LeeJaesung2/DBASEV/pixhawk/drone/roadData/real_test_data/road_id7_data.xlsx

road_id | waypoint_id | latitude(위도) | longtitude(경도) | altitude
7 | 1 | 35.1544175 | 128.1048654 | 3
7 | 2 | 35.1543759 | 128.1048862 | 3
7 | 3 | 35.1543342 | 128.104907 | 3
7 | 4 | 35.1542926 | 128.1049278 | 3
7 | 5 | 35.1542509 | 128.1049486 | 3
