LeeJaesung2/DBASEV/pixhawk/Documentation/3.getAttribute.py

# 속성 값 설명 링크 : https://dronekit-python.readthedocs.io/en/latest/automodule.html#dronekit.Vehicle.armed
from dronekit import connect, VehicleMode
import time

# 기본 시작 코드
vehicle = connect("/dev/ttyAMA0", wait_ready=True, baud=57600)
vehicle.mode = VehicleMode("GUIDED")
vehicle.armed = True
while not vehicle.mode.name =='GUIDED' and not vehicle.armed and not api.exit:
    print (" Getting ready to take off ...")
    time.sleep(1)
    
# vehicle is an instance of the Vehicle class
print ("Autopilot Firmware version: %s" % vehicle.version)
print ("Autopilot capabilities (supports ftp): %s" % vehicle.capabilities.ftp)
print ("Global Location: %s" % vehicle.location.global_frame)
print ("Global Location (relative altitude): %s" % vehicle.location.global_relative_frame)
print ("Local Location: %s" % vehicle.location.local_frame)#NED
print ("Attitude: %s" % vehicle.attitude)
print ("Velocity: %s" % vehicle.velocity)
print ("GPS: %s" % vehicle.gps_0)
print ("Groundspeed: %s" % vehicle.groundspeed)
print ("Airspeed: %s" % vehicle.airspeed)
print ("Gimbal status: %s" % vehicle.gimbal)
print ("Battery: %s" % vehicle.battery)
print ("EKF OK?: %s" % vehicle.ekf_ok)
print ("Last Heartbeat: %s" % vehicle.last_heartbeat)
print ("Rangefinder: %s" % vehicle.rangefinder)
print ("Rangefinder distance: %s" % vehicle.rangefinder.distance)
print ("Rangefinder voltage: %s" % vehicle.rangefinder.voltage)
print ("Heading: %s" % vehicle.heading)
print ("Is Armable?: %s" % vehicle.is_armable)
print ("System status: %s" % vehicle.system_status.state)
print ("Mode: %s" % vehicle.mode.name) # settable
print ("Armed: %s" % vehicle.armed) # settable
