LeeJaesung2/DBASEV/python_src/finaltest.py

from main import init, update
from drone import Drone
from car import Car
import time

# straight
'''
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
    car_idx += 1

    update_time = time.time()
    log_data = "{},{},{},{},{},{},{},{}\n".format(update_time-starttime,car.velocity,car.road_id,car.waypoint,drone.velocity,drone.current_speed,drone.road_id,drone.target_waypoint)
    add_logfile(log_data)
    time.sleep(0.1)    
