LeeJaesung2/DBASEV/test/messageQueue/messageQueue.cpp

#include "messageQueue.h"
#include <Python.h>

#include <iostream> //cout
#include <string>
#include <cstring>
#include <cstdlib>
#include <unistd.h>
#include <sys/ipc.h>
#include <sys/msg.h>


#define BUFFER_SIZE 26

int pushcount = 0;
int fullcount = 0;

int callPython(const char *src,const char *func, int arg, ...){
    PyObject *pName, *pModule, *pFunc;
    PyObject *pArgs, *pValue;
    int i;

    Py_Initialize();
    PyRun_SimpleString("import sys");
    PyRun_SimpleString("sys.path.append(\".\")");
    pName = PyUnicode_DecodeFSDefault(src); //get python src

    /*Error checking of pName*/
    pModule = PyImport_Import(pName);
    Py_DECREF(pName);

    if (pModule != NULL) {
        pFunc = PyObject_GetAttrString(pModule, func);

        if (pFunc && PyCallable_Check(pFunc)) {

            va_list ap;
            va_start(ap,arg);
            pArgs = PyTuple_New(arg);
            for (i = 0; i < arg; ++i) {
                pValue = PyLong_FromLong(va_arg(ap,int));
                if (!pValue) {
                    Py_DECREF(pArgs);
                    Py_DECREF(pModule);
                    fprintf(stderr, "Cannot convert argument\n");
                    return 1;
                }
                /* pValue reference stolen here: */
                PyTuple_SetItem(pArgs, i, pValue);
            }
            pValue = PyObject_CallObject(pFunc, pArgs); // call function with argument
            Py_DECREF(pArgs);
            /*value checking*/
            if (pValue != NULL) {
                printf("Result of call: %ld\n", PyLong_AsLong(pValue));
                Py_DECREF(pValue);
            }
            /*No return value*/
            else {
                Py_DECREF(pFunc);
                Py_DECREF(pModule);
                PyErr_Print();
                fprintf(stderr,"Call failed\n");
                return 1;
            }
            va_end(ap);
        }
        else {
            if (PyErr_Occurred())
                PyErr_Print();
            fprintf(stderr, "Cannot find function \"%s\"\n", func);
        }
        Py_XDECREF(pFunc);
        Py_DECREF(pModule);
    }
    else {
        PyErr_Print();
        fprintf(stderr, "Failed to load \"%s\"\n", src);
        return 1;
    }
    Py_Finalize();
    return PyLong_AsLong(pValue);
    
}

using namespace std;

struct MsgBuf {
    long msgtype; // message type, must be > 0
    int value;
    char buf[BUFFER_SIZE];
};

int mq_init(key_t key){

    int key_id = msgget( key, IPC_CREAT|0666);
    if (key_id == -1) {
        cerr << "Message Get Failed!" << endl;
        exit(EXIT_FAILURE);
    }
    return key_id;
}

void push(int key_id,msqid_ds buf, MsgBuf msg){
    

    pushcount++;
    if (msgctl(key_id, IPC_STAT, &buf) == -1) {
        std::cerr << "Failed to get message queue status!" << std::endl;
        return;
    }
    //Check queue is full
    if (buf.msg_qnum >= 409) {
        std::cerr << "Message queue is full. Skipping message send." << std::endl;
        usleep(1);
        return;
    }
    // Check the number of messages currently in the queue
    printf("num of data in the queue is %ld\n",buf.msg_qnum);
    while (buf.msg_qnum >0 ) {
        // Remove existing message before pushing a new one
        if (msgrcv(key_id, &msg, sizeof(msg), 0, IPC_NOWAIT) == -1) {
            std::cerr << "Failed to remove existing message from the queue!" << std::endl;
            return;
        }
    }
    if (msgsnd(key_id, &msg, sizeof(msg), IPC_NOWAIT) == -1) {
            cerr << "Message Sending Failed!" << endl;
            exit(EXIT_FAILURE);
        }
}

void * comm(void *arg){
    int cnt = 0;
    MsgBuf msg;
    msg.msgtype = 1;
    int key_id = mq_init((key_t)5657);

    struct msqid_ds buf;
    while(1){
        msg.value = ++cnt;
        if (cnt >= 100000) {
            cout << "Message Sending Finished!" << endl;
            break;
        }
        strcpy(msg.buf, "Message received!]");
        push(key_id,buf, msg);
        cout << "value: " << msg.value << endl;
        //sleep(1);

    }
    //sleep(10);
    cout <<"full counter" << fullcount << endl;
    cout <<"push counter" << pushcount << endl;
    return 0;
}


void * producer(void *arg){
    // int cnt = 0;
    // int key_id;
    // MsgBuf msg;
    // msg.msgtype = 1;

    // key_id = msgget((key_t) 7777, IPC_CREAT|0666);
    // printf("queue key id is %d\n",key_id);
    // if (key_id == -1) {
    //     cerr << "Message Get Failed!" << endl;
    //     exit(EXIT_FAILURE);
    // }
    
    // while (1) {
    //     msg.value = ++cnt;
    
    //     if (cnt >= 10) {
    //         cout << "Message Sending Finished!" << endl;
    //         break;
    //     }
    //     strcpy(msg.buf, "Hello from C++ producer!");
    //     if (msgsnd(key_id, &msg, sizeof(msg), IPC_NOWAIT) == -1) {
    //         cerr << "Message Sending Failed!" << endl;
    //         exit(EXIT_FAILURE);
    //     }
        
    //     cout << "value: " << msg.value << endl;
    //     sleep(1);
    // }
    // exit(EXIT_SUCCESS);
     return 0;
}

void * consumer(void *arg){
    const char *src = "consumer";
    const char *func = "consumer";
    callPython(src, func, 1, 1);   
    return 0;
}
