LeeJaesung2/DBASEV/pixhawk/drone/pixhawk_test_files/test.py

from dronekit import connect, VehicleMode, LocationGlobalRelative, Command
from pymavlink import mavutil
import time
import argparse 
import dronekit_sitl

'''
parser = argparse.ArgumentParser(description='Print out vehicle state information. Connects to SITL on local PC by default.')
parser.add_argument('--connect', 
                help="vehicle connection target string. If not specified, SITL automatically started and used.")
args = parser.parse_args()

connection_string = args.connect
sitl = None

#Start SITL if no connection string specified
if not connection_string:
    sitl = dronekit_sitl.start_default()
    connection_string = sitl.connection_string()

print("\nConnecting to vehicle on: %s" % connection_string)
vehicle = connect(connection_string, wait_ready=True)

vehicle.wait_ready('autopilot_version')
'''

connection_string = 'udp:127.0.0.1:1450'
vehicle = connect(connection_string, wait_ready=True)
print("Connecting to vehicle on : %s" %(connection_string, ))
cmd = None

# takeoff function

def arm_and_takeoff_to_pixhawk(aTargetAltitude):
    """
    Arms vehicle and fly to aTargetAltitude.
    """

    print("Basic pre-arm checks")
    # Don't try to arm until autopilot is ready
    while not vehicle.is_armable:
        print(" Waiting for vehicle to initialise...")
        time.sleep(1)

    print("Arming motors")

    # Confirm vehicle armed before attempting to take off
    while not vehicle.armed:
        print(" Waiting for arming...")
        vehicle.mode = VehicleMode("GUIDED")
        
        vehicle.armed = True
        time.sleep(1)

    print("Taking off!")
    vehicle.simple_takeoff(aTargetAltitude)  # Take off to target altitude

    while True:
        print(" Altitude: ", vehicle.location.global_relative_frame.alt)
        if vehicle.location.global_relative_frame.alt >= aTargetAltitude * 0.95:
            print("Reached target altitude")
            break
        time.sleep(1)

def add_waypoints_to_pixhawk(waypoint_list):
    
    cmd = vehicle.commands
    
    for waypoint in waypoint_list:
        print("wapoint : ", waypoint[2], waypoint[3], waypoint[4])
        wp = LocationGlobalRelative(waypoint[2], waypoint[3], waypoint[4])
        cmd.add(
            Command(0,0,0, 
            mavutil.mavlink.MAV_FRAME_GLOBAL_RELATIVE_ALT,
            mavutil.mavlink.MAV_CMD_NAV_WAYPOINT,
            0, 1, 0, 0, 0, 0,
            wp.lat, wp.lon, wp.alt
            )
        )    
    cmd.upload()
    
    change_vehicleMode("AUTO")

    cmd.next = 0

def print_current_gps():
    current_gps = vehicle.location.global_frame
    print("위도: %.7f" % current_gps.lat)
    print("경도: %.7f" % current_gps.lon)
    print("고도: %.1f" % current_gps.alt)
    

def set_airspeed_to_pixhawk(airspeed):
    vehicle.groundspeed = airspeed


def change_vehicleMode(new_mode):
    while vehicle.mode.name != new_mode:
        print("Vehicl mode : ", vehicle.mode.name)
        print("Changing Vehcile mode to ", new_mode, "....")
        
        vehicle.mode = VehicleMode(new_mode)
        time.sleep(1)


def land_to_pixhawk(vehicle):
    vehicle.mode = VehicleMode("LAND") 
    while not vehicle.mode.name=='LAND':
        print("Waiting for drone to land...")
        time.sleep(1)

    vehicle.armed = False 
    vehicle.close() 

"""------------------------------------------------------------------------------------"""
'''
# curve course
waypoints = {1: [[1, 1, 35.1535098, 128.1002861, 5.0], [1, 2, 35.1535017, 128.1003405, 5.0], [1, 3, 35.153494, 128.1003952, 5.0], [1, 4, 
35.1534847, 128.1004491, 5.0], [1, 5, 35.153477, 128.1005038, 5.0], [1, 6, 35.1534693, 128.1005578, 5.0], [1, 7, 35.1534608, 
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


def test():
    start_time = time.time()
    arm_and_takeoff_to_pixhawk(5.0)
    
    add_waypoints_to_pixhawk(waypoints[1])

    set_airspeed_to_pixhawk(1)

test()
